jharvey/Solar_Kit/Simulations/MOS_Heat_Test2/MOS_HEAT_TEST-PSpiceFiles/Testbench/trans/trans.cir

** Profile: "Testbench-trans"  [ c:\users\mypc\desktop\solar_kit\simulations\mos_heat_test2\mos_heat_test-pspicefiles\testbench\trans.sim ] 

** Creating circuit file "trans.cir" 
** WARNING: THIS AUTOMATICALLY GENERATED FILE MAY BE OVERWRITTEN BY SUBSEQUENT SIMULATIONS

*Libraries: 
* Profile Libraries :
* Local Libraries :
* From [PSPICE NETLIST] section of C:\cds_spb_home\cdssetup\OrCAD_PSpiceTIPSpice_Install\17.4.0\PSpice.ini file:
.lib "nom_pspti.lib" 
.lib "nom.lib" 

*Analysis directives: 
.TRAN  0 40us 0 
.OPTIONS ADVCONV
.OPTIONS FILEMODELSEARCH
.PROBE64 V(alias(*)) I(alias(*)) W(alias(*)) D(alias(*)) NOISE(alias(*)) 
.INC "..\Testbench.net" 


.END
