jharvey/Solar_Kit/Simulations/DC-DC_LTSpice/LLC-ZVS_Boost.asc

C1: polcap; {Cr}; V=100 Irms=1.88 Rser=0.013 Lser=6.47n mfg="Würth Elektronik" pn="860040880011 WCAP-ATUL 16x35,5" type="Al electrolytic"
C2: polcap; 0.04µ; V=100 Irms=1.88 Rser=0.013 Lser=6.47n mfg="Würth Elektronik" pn="860040880011 WCAP-ATUL 16x35,5" type="Al electrolytic"
D1: diode
D2: diode
L1: ind; {Lm}; Ipk=2.64 Rser=0.353 Rpar=34207.5 Cpar=0 mfg="Bourns, Inc." pn="SRF1280-470M-series"
L2: ind; {Lk}; Ipk=17.2 Rser=0.01313 Rpar=21316 Cpar=20.57p mfg="Würth Elektronik" pn="7443783533650 WE-HCFT 3533"
L3: ind; {Lr}; Ipk=17.2 Rser=0.01313 Rpar=21316 Cpar=20.57p mfg="Würth Elektronik" pn="7443783533650 WE-HCFT 3533"
LP1: ind2; {Lp}
LS1: ind2; {Ls}
LS2: ind2; {Ls}
Q2: nmos; IRFH5207
Q3: nmos; IRFH5207
R1: res; 1000
R2: res; 100
R3: res; 100
R4: res; 10k
R5: res; 10k
R6: res; {Rts}
R7: res; {Rts}
R8: res; {Rtp}
V1: voltage; 36; Rser=0.01 Cpar=0.1u
V2: voltage; PULSE(0 5 {Ton} 16n 16n {Tonlow} {Tperiod})
V3: voltage; PULSE(0 5 0 16n 16n {Ton} {Tperiod})
Named nets: 0, Vout, Vhi_g, Vlo_g, Vmid, Vhp, Vlp, Vsup, Vt+, Vt-, Vtrans
.tran 0.5ms startup
K1 LP1 LS1 LS2 1.00
.param Lp=2.5u
.param Turns=1/18
.param Ls=Lp/PWR(Turns,2)
.param Cr=6.2n
.param Lr=62.1u
.param Lk=100n
.param Lm=149.2u
.param SwFreq=1/(2*pi*sqrt((Lr+Lk)*Cr))
.param Tperiod=1/SwFreq
.param Ton=Tperiod*0.5
.param Tonlow=Tperiod-Ton
.param Rtp=0.005
.param Rts=0.250
Lp is transformer primary inductance
Turns is the turns ratio
Ls is the transformer secondary inductance
Cr is the C from LLC topology
Lr is one of the L's from LLC topology
Lk is the transformer leakage inductance
Lm is the magnetization inductance, simulatin the inrush 
SwFreq is the Switching Frequency (256khz)
Tperiod is the period of the frequency, this is 50% duty.
Ton is the high side on time
Tonlow is the low side on time
Rtp is the transformer primary winding resistance
Rts is the transformer secondary winding resistance
Vtrans peaks around 1kV
50.3W is R1 power
65.5W is Lp power
Perhaps using Digikey 732-2131-ND
Which has a 10:1 while this needs more like 1:10
 
Ref
https://www.ti.com/lit/ug/tiduct9a/tiduct9a.pdf
