jharvey/Solar_Kit/Simulations/MOS_Heat_LTSpice/MOSFET_Heat_Sim_Pulse.asc

C1: cap; 470µ
L1: ind; 64µ
M1: nmos; IPB027N10N3
M2: nmos; IPB027N10N3
R1: res; 1
R2: res; 1
R3: res; 1
R4: res; 100k
R5: res; 100k
R6: res; 0.01
V1: voltage; 24; Rser=0.01 Cpar=0.1u
V2: voltage; PULSE(0 30 0.15u 16n 16n 0.15u 0.25u)
V3: voltage; PULSE(0 30 0 16n 16n 0.15u 0.25u)
Named nets: 0, Vout, Vhi_g, Vlo_g, Vmid, Vhp, Vlp
.tran 1ms startup
